gili-yankovitch/SwordOfSecrets/images/sword.png

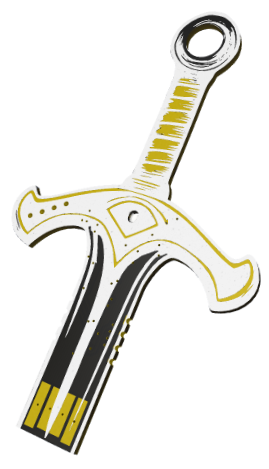
images/sword.png
